Audio-Rochey/Terrain-Tronics-Caernarfon-Castle/Demo-FallingFloors/buttonfunctions.h

#ifndef buttonfunctions_H
#define buttonfunctions_H
#include <Arduino.h>
#include <Servo.h>



void ledUpdate();
void buttonZERO();
void buttonONE();
void buttonTWO();
void buttonTHREE();
void buttonFOUR();
void buttonFIVE();
void buttonSIX();
void buttonSEVEN();
void buttonEIGHT();
void buttonNINE();








#endif
